whowechina/iidx_pico/cad/kailh-choc-stibilizer-4.jpg

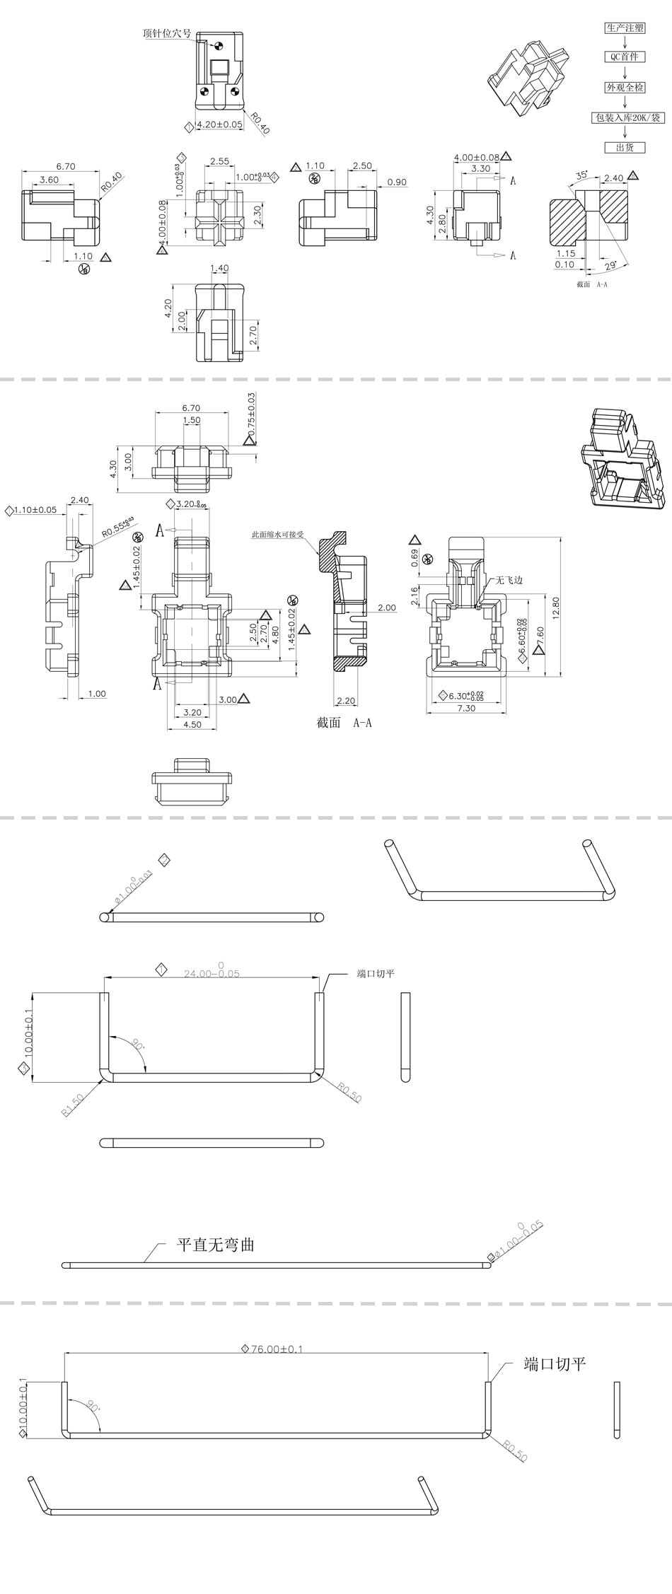
cad/kailh-choc-stibilizer-4.jpg
