whowechina/iidx_pico/PCB/Itsy/3dmodels/WS2812B.step

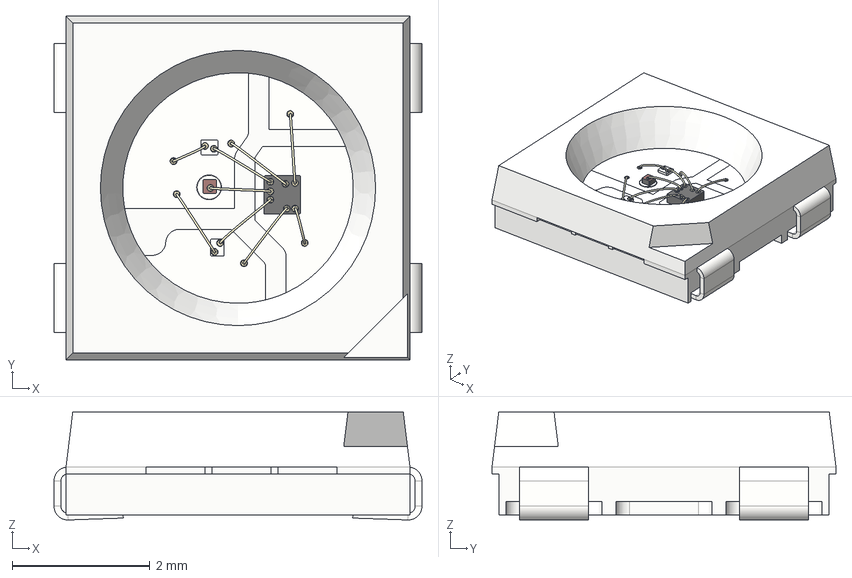
[picture p52: CAD file, 2023-04-01]
PCB/Itsy/3dmodels/WS2812B.step
5.35 x 5.00 x 1.57 mm
