whowechina/iidx_pico/PCB/Pico/3dmodels/SM3B-SRSS-TB.step

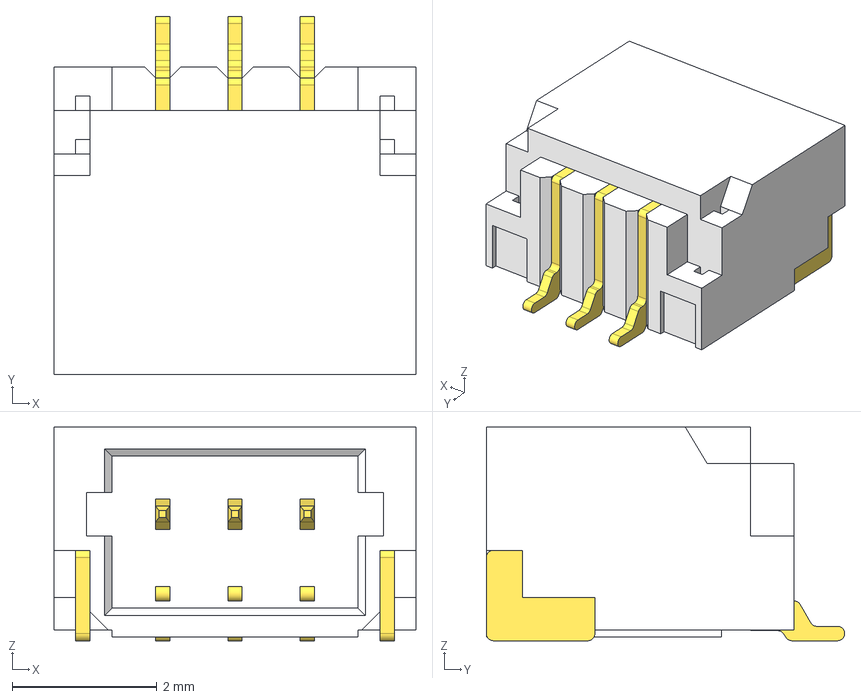
[picture p53: CAD file, 2024-11-20]
PCB/Pico/3dmodels/SM3B-SRSS-TB.step
5.00 x 4.95 x 2.95 mm
