whowechina/iidx_pico/Production/AcrylicCut/TT_disc_170.dxf

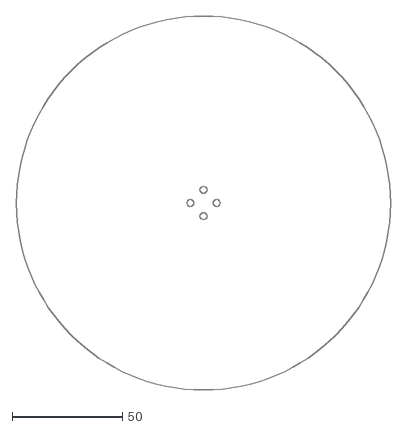
[picture p54: CAD file, 2023-04-01]
Production/AcrylicCut/TT_disc_170.dxf
170.0 x 170.0
