whowechina/iidx_pico/cad/keycap_frame_aux.stl

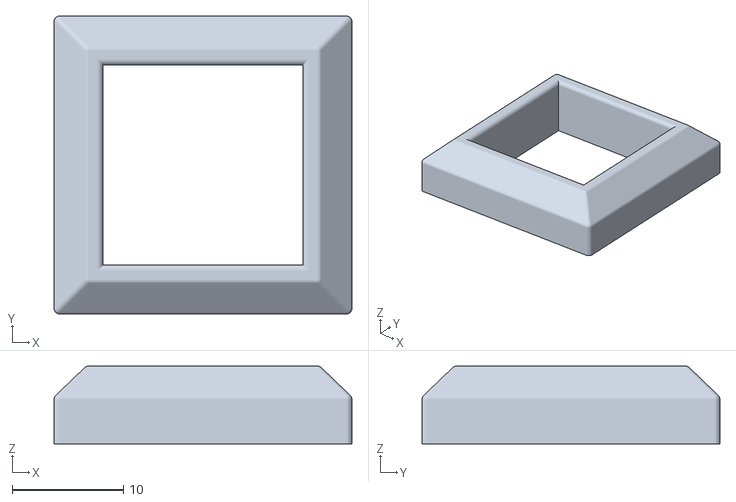
[picture p55: CAD file, 2023-04-01]
cad/keycap_frame_aux.stl
26.8 x 26.8 x 7.00
