whowechina/iidx_pico/Production/AcrylicCut/TT_disc_180.dxf

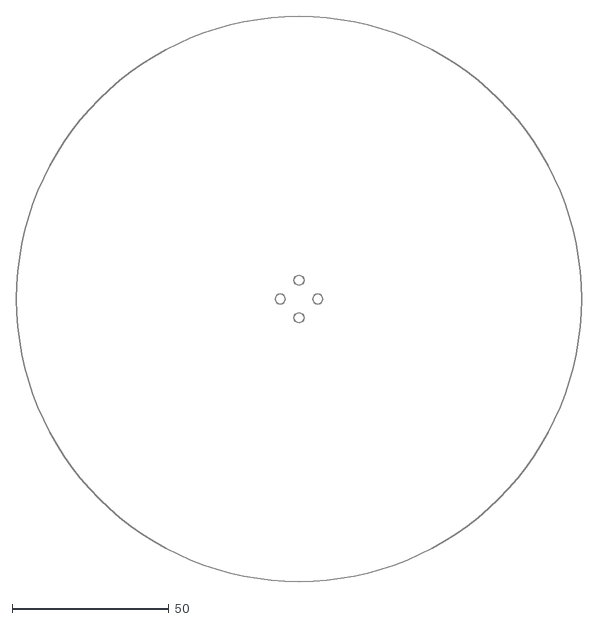
[picture p57: CAD file, 2023-04-01]
Production/AcrylicCut/TT_disc_180.dxf
180.0 x 180.0
