whowechina/iidx_pico/cad/pogo5f.stl

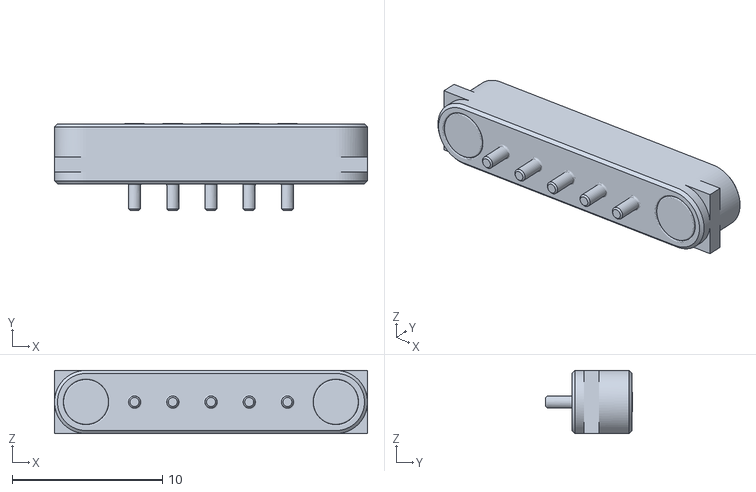
[picture p58: CAD file, 2023-04-01]
cad/pogo5f.stl
20.8 x 5.75 x 4.20
