whowechina/iidx_pico/PCB/Itsy/3dmodels/Magnetic Pogo Connector 5 Pin (M) - 副本.STEP

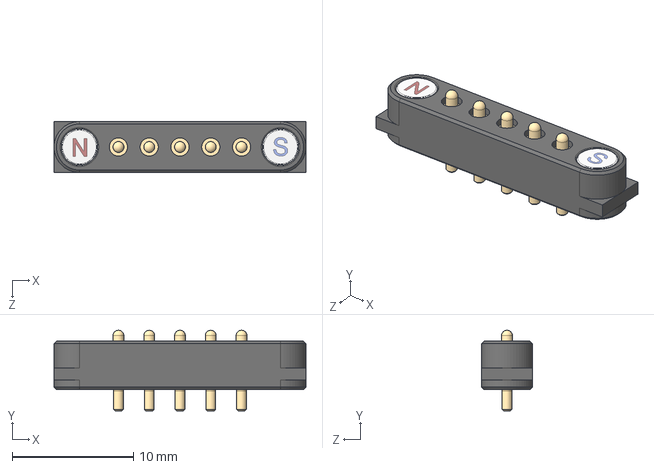
[picture p59: CAD file, 2023-04-01]
PCB/Itsy/3dmodels/Magnetic Pogo Connector 5 Pin (M) - 副本.STEP
20.8 x 6.65 x 4.20 mm
