whowechina/iidx_pico/Production/3DPrint/Turntable Itsy - Disc.stl

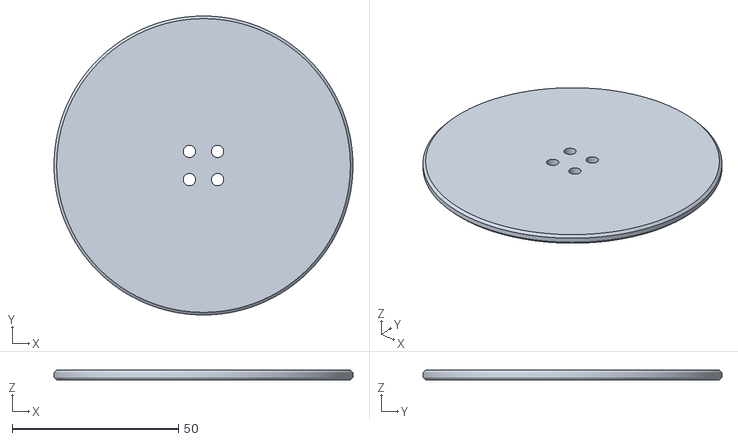
[picture p60: CAD file, 2026-05-16]
Production/3DPrint/Turntable Itsy - Disc.stl
90.0 x 90.0 x 3.00
