whowechina/iidx_pico/Production/AcrylicCut/TT_disc_150.dxf

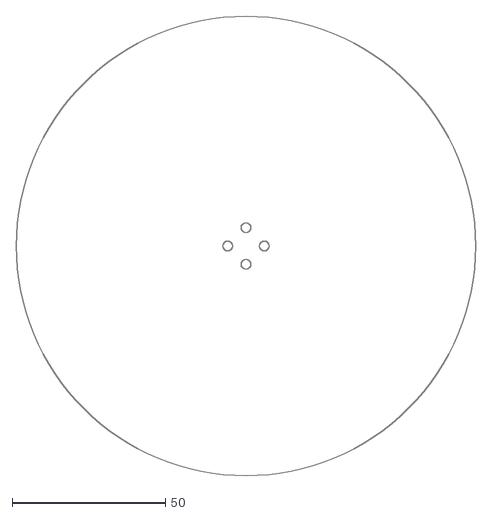
[picture p61: CAD file, 2023-04-01]
Production/AcrylicCut/TT_disc_150.dxf
150.0 x 150.0
