whowechina/iidx_pico/cad/beatmania_iidx.stl

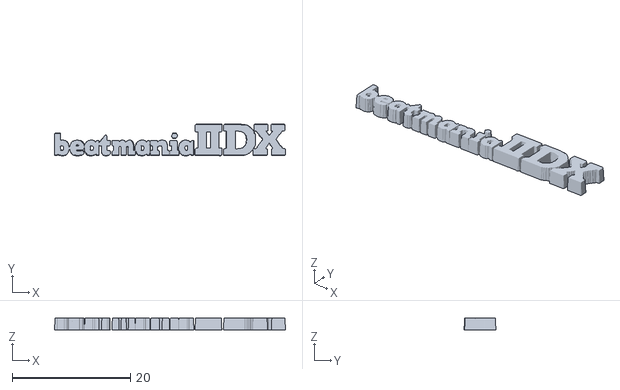
[picture p62: CAD file, 2023-04-01]
cad/beatmania_iidx.stl
39.0 x 5.38 x 2.00
