whowechina/iidx_pico/PCB/Itsy/3dmodels/SW_Hotswap_Kailh_MX.stp

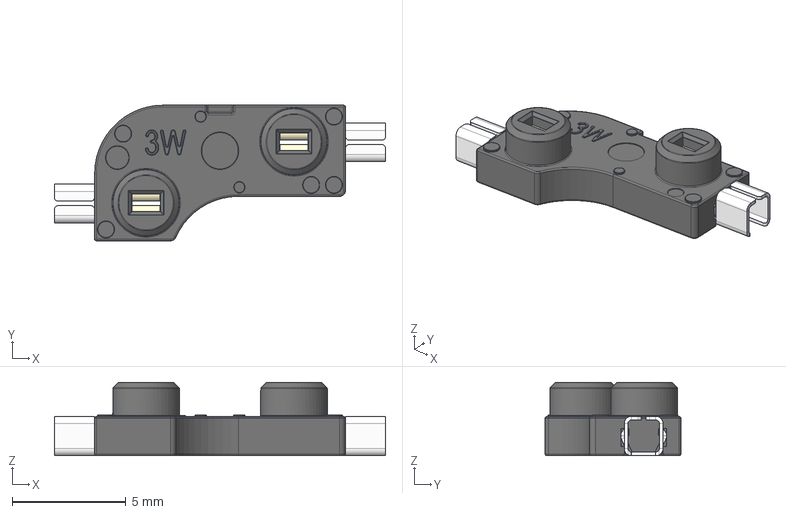
[picture p63: CAD file, 2023-04-01]
PCB/Itsy/3dmodels/SW_Hotswap_Kailh_MX.stp
14.5 x 5.95 x 3.22 mm
