whowechina/iidx_pico/Production/3DPrint/Keyboard Itsy - Base_1P.stl

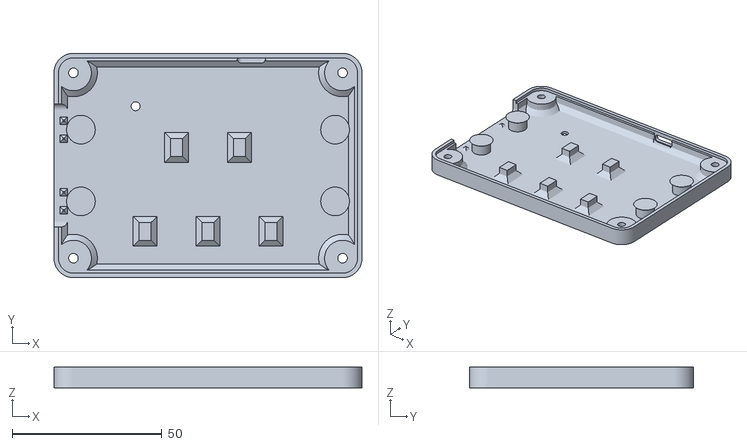
[picture p64: CAD file, 2026-05-16]
Production/3DPrint/Keyboard Itsy - Base_1P.stl
103.0 x 75.0 x 7.00
