whowechina/iidx_pico/PCB/Itsy/3dmodels/Magnetic Pogo Connector 5 Pin (Type 3).STEP

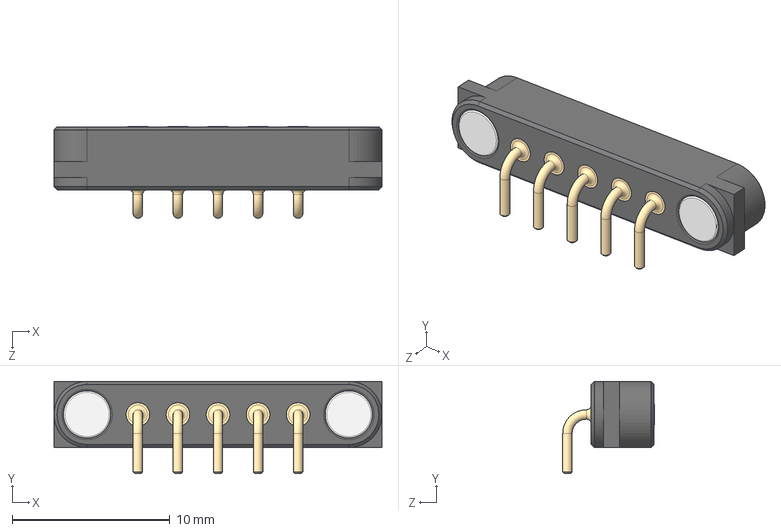
[picture p65: CAD file, 2023-04-01]
PCB/Itsy/3dmodels/Magnetic Pogo Connector 5 Pin (Type 3).STEP
20.8 x 5.85 x 5.80 mm
