whowechina/iidx_pico/Production/3DPrint/Keyboard Itsy - Panel.stl

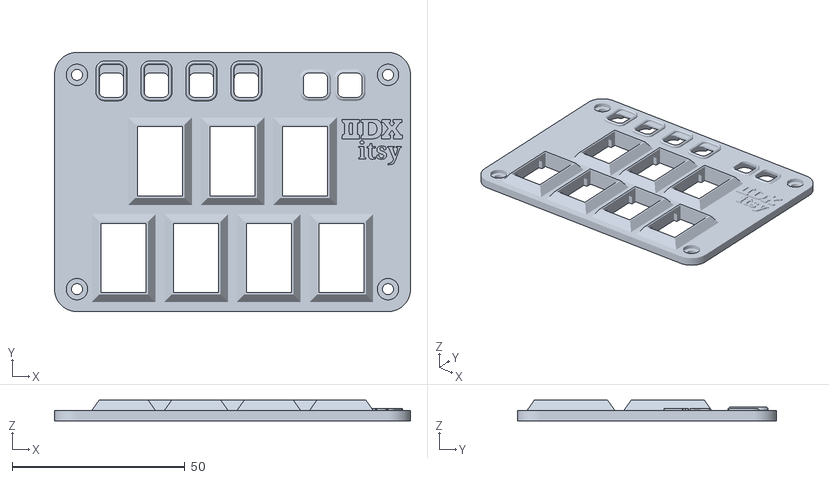
[picture p66: CAD file, 2026-05-16]
Production/3DPrint/Keyboard Itsy - Panel.stl
103.0 x 75.0 x 6.00
