whowechina/iidx_pico/cad/skf6805.stl

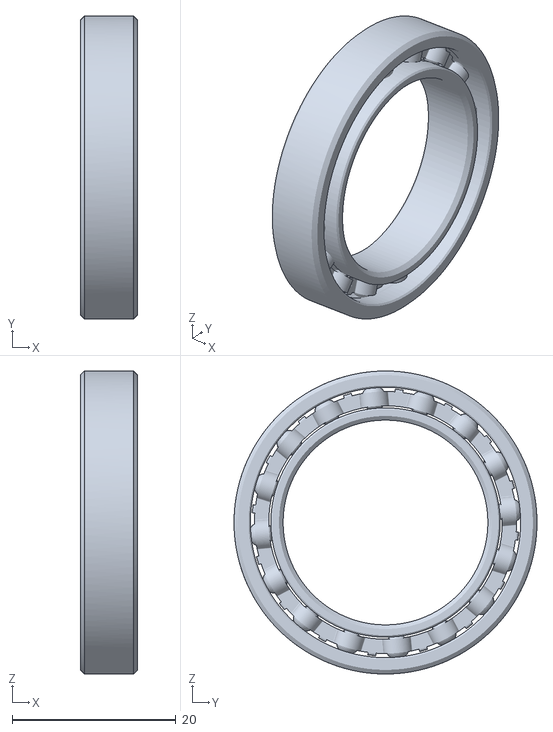
[picture p67: CAD file, 2023-04-01]
cad/skf6805.stl
7.00 x 37.0 x 37.0
