whowechina/iidx_pico/PCB/Itsy/3dmodels/J 2835.step

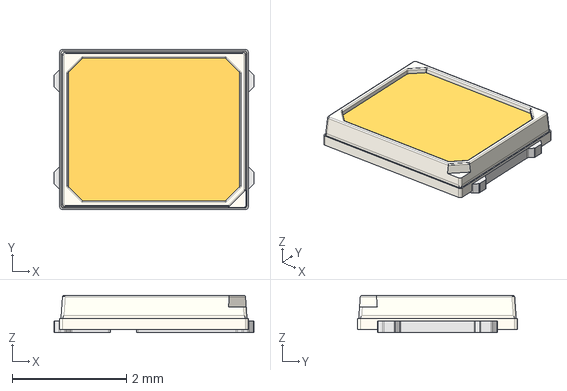
[picture p68: CAD file, 2023-04-01]
PCB/Itsy/3dmodels/J 2835.step
3.50 x 2.80 x 0.65 mm
