whowechina/iidx_pico/Production/3DPrint/Turntable Itsy - Banner.stl

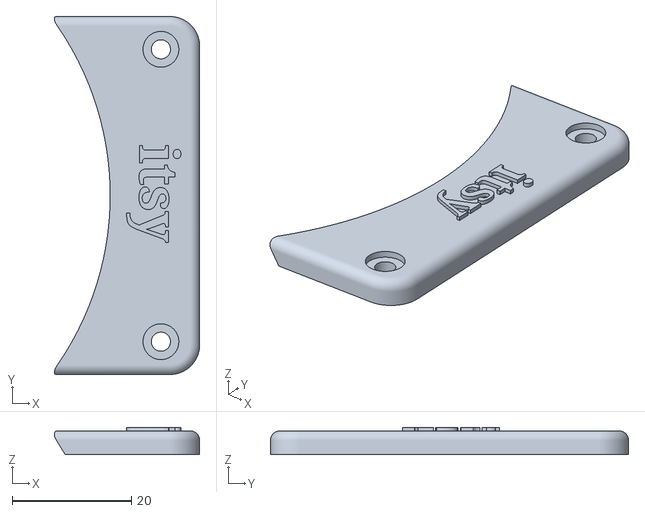
[picture p69: CAD file, 2026-05-16]
Production/3DPrint/Turntable Itsy - Banner.stl
24.4 x 60.0 x 4.60
