whowechina/iidx_pico/PCB/Itsy/3dmodels/WS2812-0807.STEP

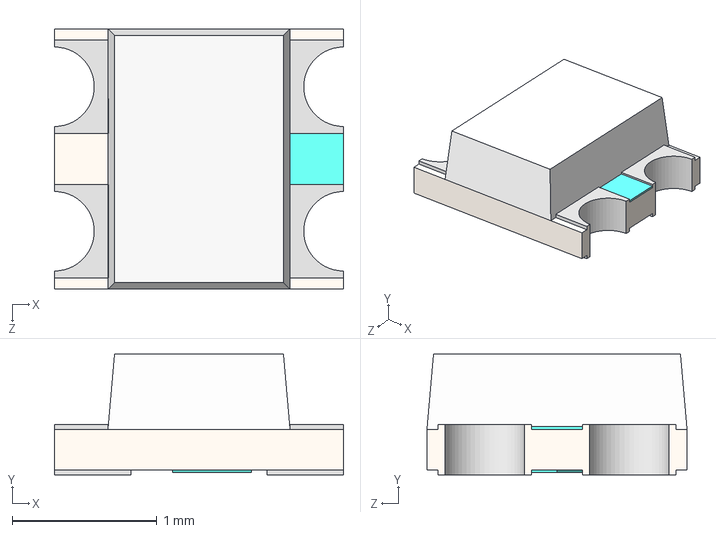
[picture p70: CAD file, 2023-04-01]
PCB/Itsy/3dmodels/WS2812-0807.STEP
2.00 x 0.835 x 1.80 mm
