whowechina/iidx_pico/PCB/Itsy/3dmodels/SW_Kailh_Choc_V1.stp

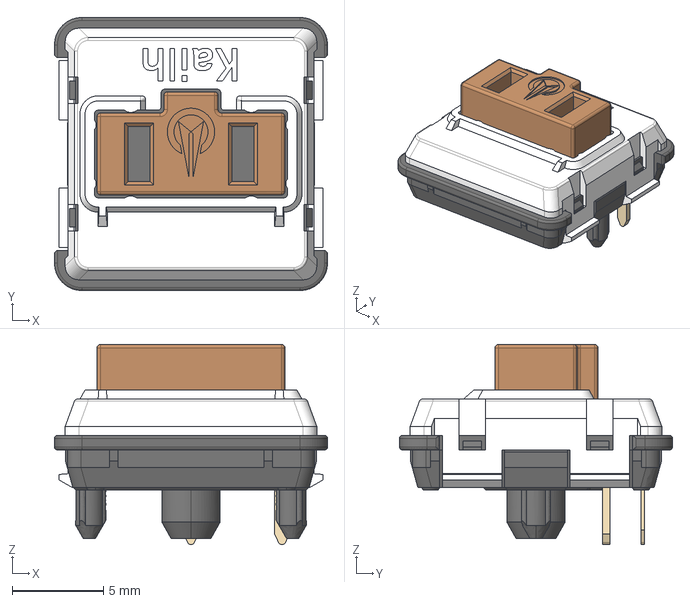
[picture p71: CAD file, 2023-04-01]
PCB/Itsy/3dmodels/SW_Kailh_Choc_V1.stp
15.0 x 15.0 x 11.0 mm
