whowechina/iidx_pico/Production/3DPrint/Keycap Itsy - Keycap.stl

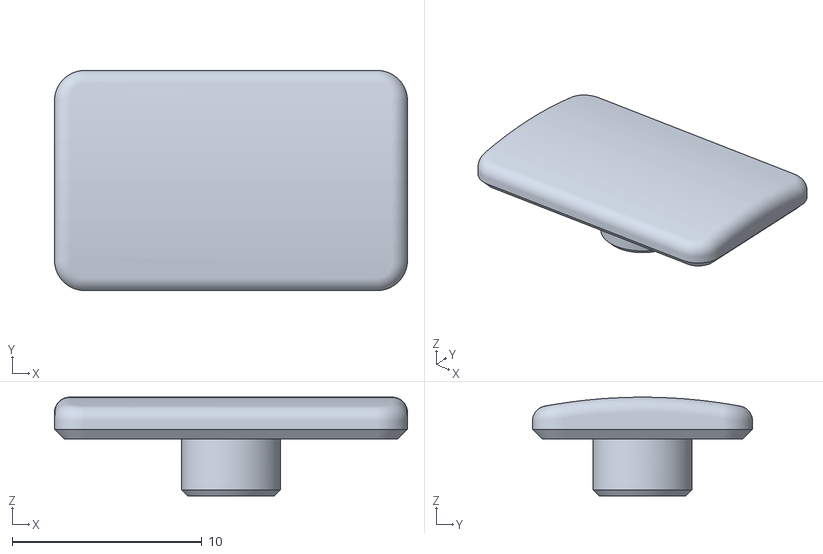
[picture p72: CAD file, 2026-05-16]
Production/3DPrint/Keycap Itsy - Keycap.stl
18.6 x 11.6 x 5.20
