whowechina/iidx_pico/PCB/Itsy/3dmodels/User Library-PTS645SL95SMTR92-LFS.STEP

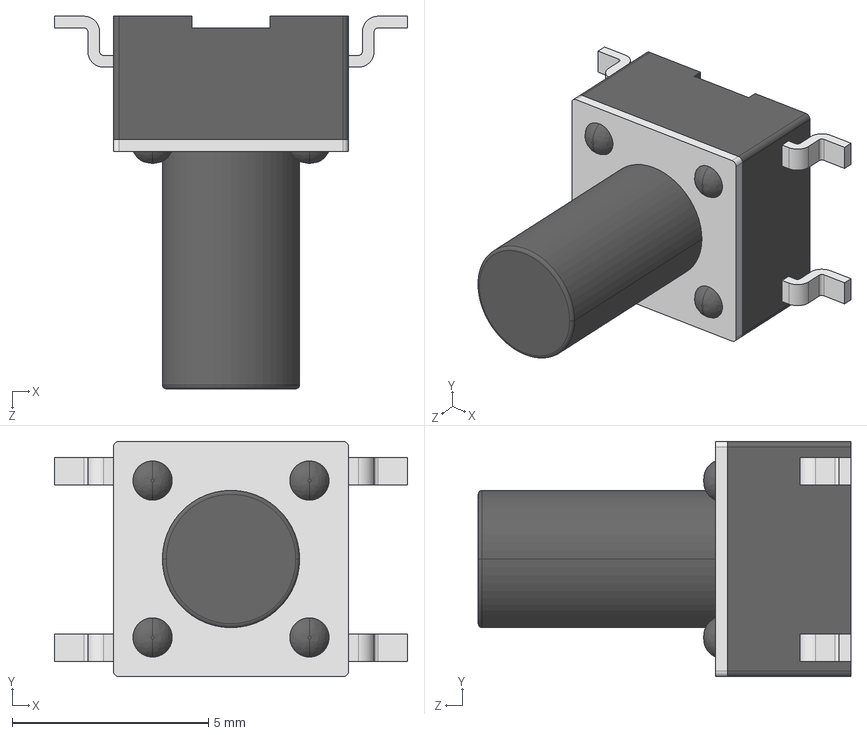
[picture p73: CAD file, 2023-04-01]
PCB/Itsy/3dmodels/User Library-PTS645SL95SMTR92-LFS.STEP
9.00 x 6.00 x 9.50 mm
