whowechina/iidx_pico/Production/3DPrint/Turntable Itsy - Base.stl

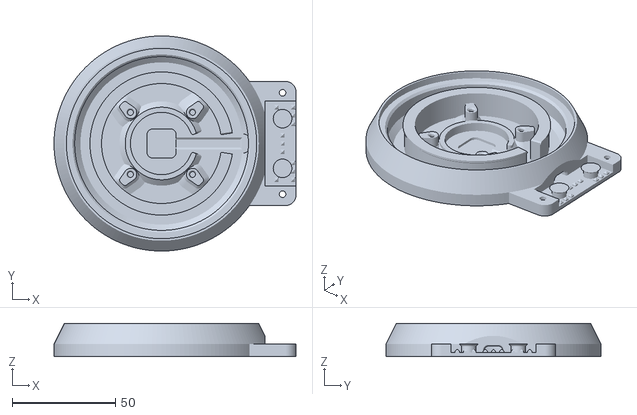
[picture p74: CAD file, 2026-05-16]
Production/3DPrint/Turntable Itsy - Base.stl
117.0 x 104.0 x 16.0
