whowechina/iidx_pico/PCB/Itsy/3dmodels/EVQ-P1D05M.stp

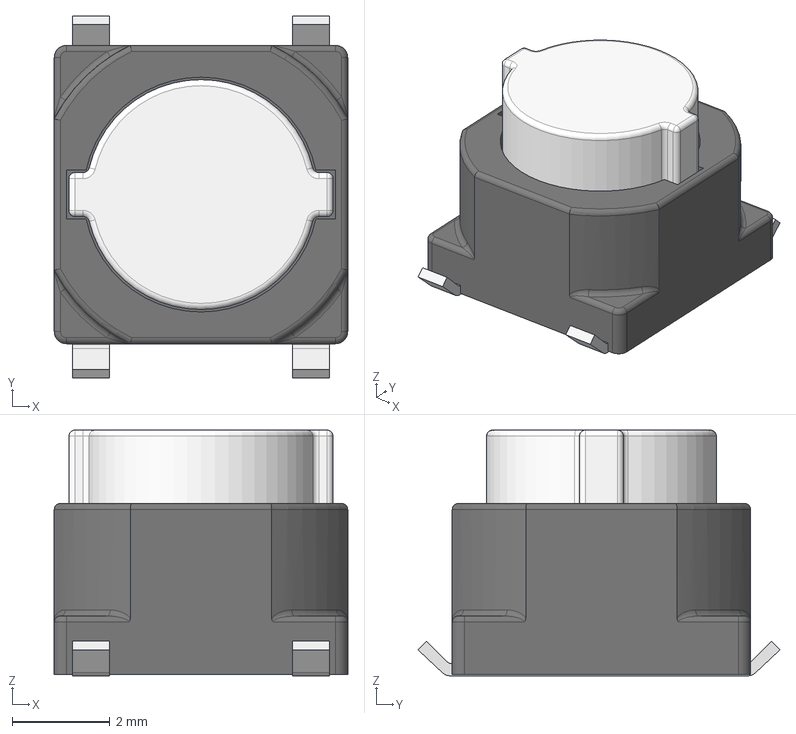
[picture p75: CAD file, 2023-04-01]
PCB/Itsy/3dmodels/EVQ-P1D05M.stp
6.00 x 7.40 x 5.03 mm
