whowechina/iidx_pico/Production/3DPrint/Turntable Jumbo - Disc.stl

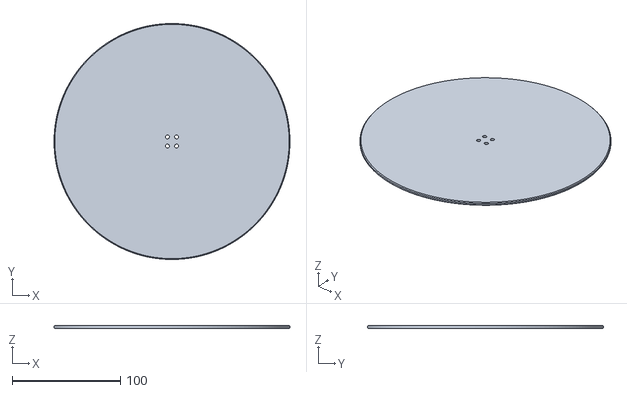
[picture p76: CAD file, 2026-03-05]
Production/3DPrint/Turntable Jumbo - Disc.stl
218.0 x 218.0 x 3.00
