whowechina/iidx_pico/PCB/Itsy/3dmodels/SMD WS2812B-3535.step

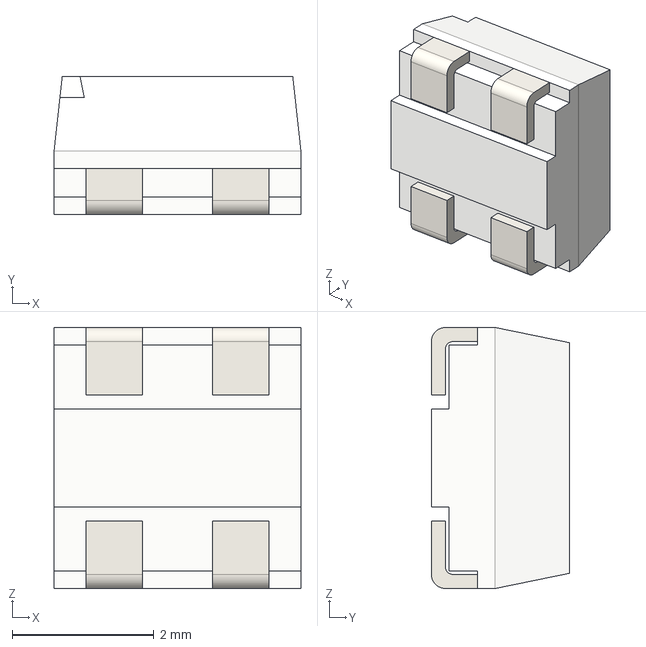
[picture p77: CAD file, 2023-04-01]
PCB/Itsy/3dmodels/SMD WS2812B-3535.step
3.48 x 1.95 x 3.68 mm
