whowechina/iidx_pico/Production/3DPrint/Turntable Teeny - Disc.stl

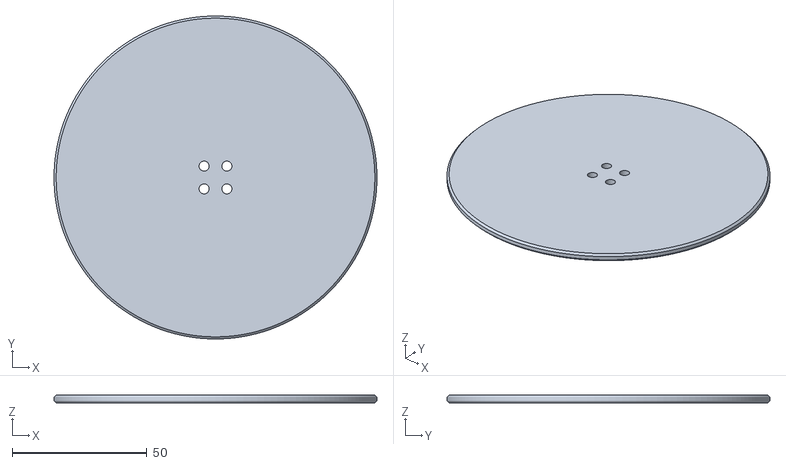
[picture p78: CAD file, 2026-03-05]
Production/3DPrint/Turntable Teeny - Disc.stl
120.0 x 120.0 x 3.00
