whowechina/iidx_pico/PCB/Itsy/3dmodels/User Library-WS2812-2020.step

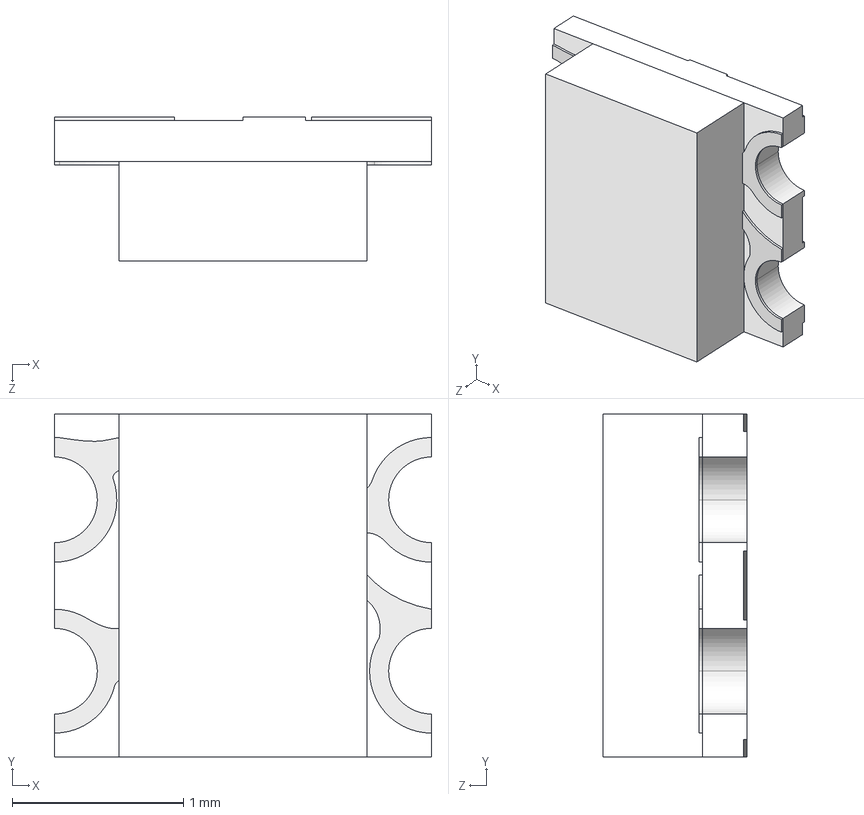
[picture p79: CAD file, 2023-04-01]
PCB/Itsy/3dmodels/User Library-WS2812-2020.step
2.20 x 2.00 x 0.84 mm
