whowechina/iidx_pico/Production/3DPrint/Turntable Pico - Disc.stl

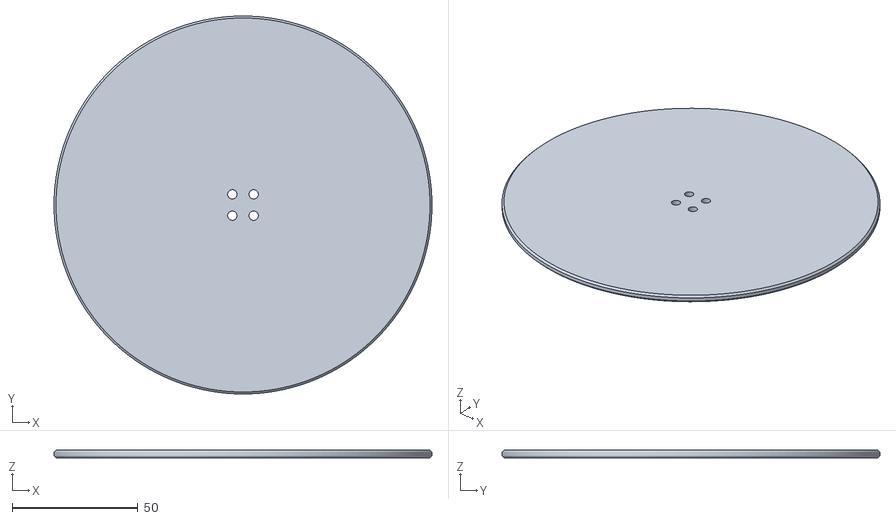
[picture p80: CAD file, 2026-03-05]
Production/3DPrint/Turntable Pico - Disc.stl
150.0 x 150.0 x 3.00
