whowechina/iidx_pico/PCB/Itsy/3dmodels/Kailh LP Choc PC Keycap.step

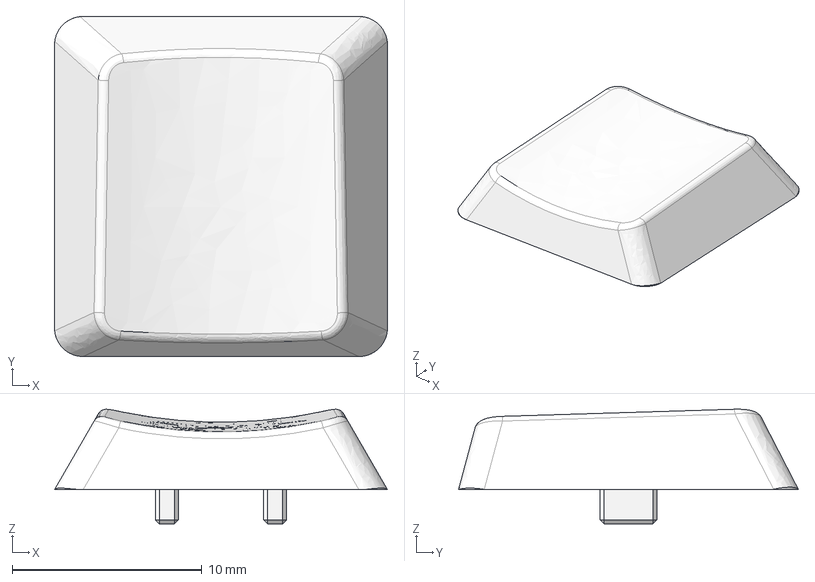
[picture p81: CAD file, 2023-04-01]
PCB/Itsy/3dmodels/Kailh LP Choc PC Keycap.step
17.5 x 17.9 x 6.03 mm
