whowechina/iidx_pico/Production/3DPrint/Turntable Jumbo 1P - Banner.stl

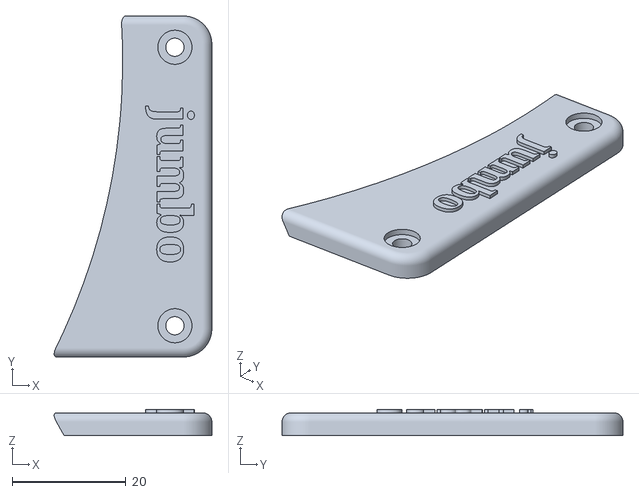
[picture p82: CAD file, 2025-11-17]
Production/3DPrint/Turntable Jumbo 1P - Banner.stl
27.7 x 60.0 x 4.60
