whowechina/iidx_pico/PCB/Itsy/3dmodels/User Library-WS2812-4020.step

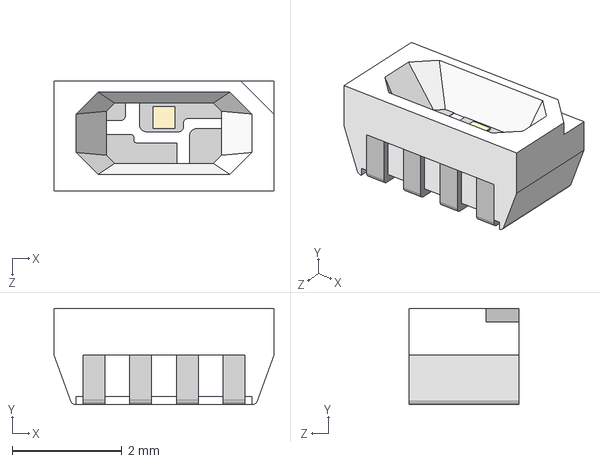
[picture p83: CAD file, 2023-04-01]
PCB/Itsy/3dmodels/User Library-WS2812-4020.step
4.00 x 1.75 x 2.00 mm
