whowechina/iidx_pico/Production/3DPrint/Turntable Teeny - Banner.stl

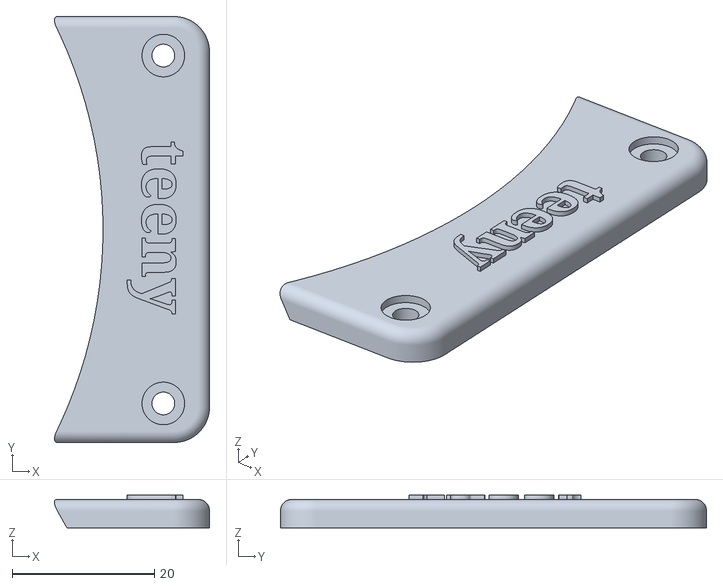
[picture p84: CAD file, 2025-11-17]
Production/3DPrint/Turntable Teeny - Banner.stl
21.8 x 60.0 x 4.60
