whowechina/iidx_pico/PCB/Itsy/3dmodels/WS2812-2020.STEP

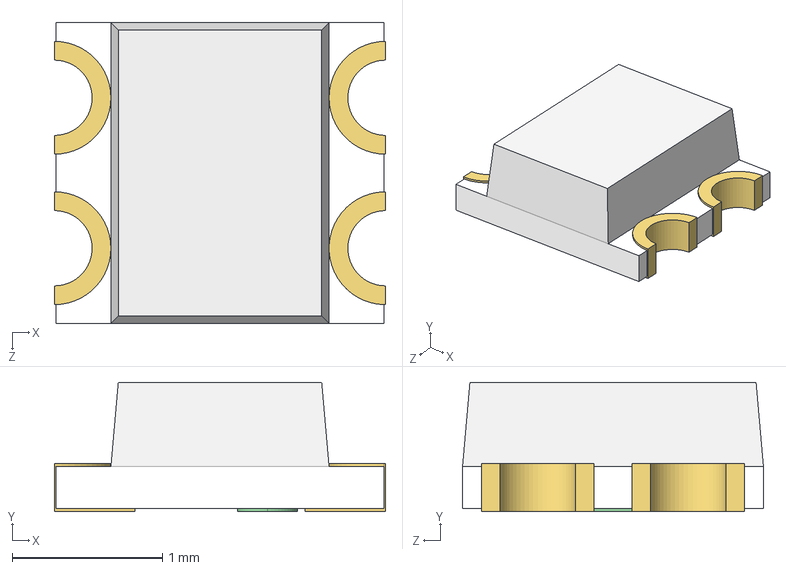
[picture p85: CAD file, 2023-04-01]
PCB/Itsy/3dmodels/WS2812-2020.STEP
2.20 x 0.86 x 2.00 mm
