whowechina/iidx_pico/Production/3DPrint/Keyboard DP - Base.stl

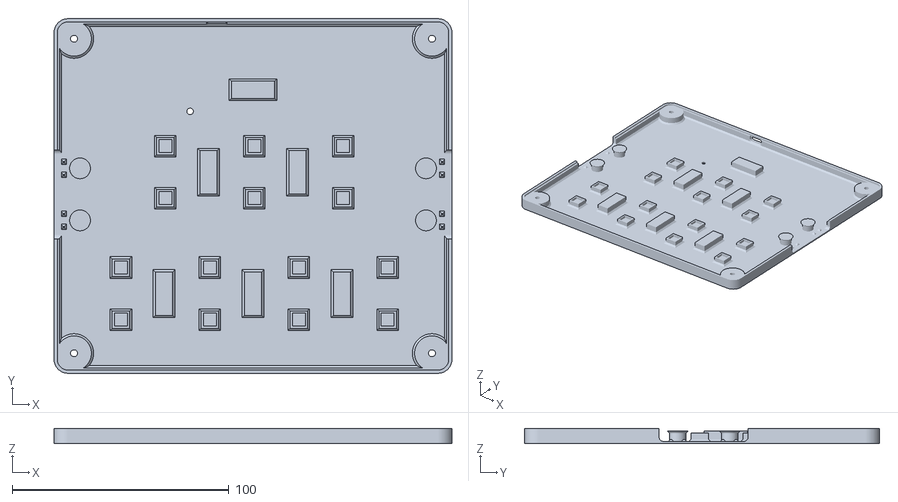
[picture p86: CAD file, 2025-11-17]
Production/3DPrint/Keyboard DP - Base.stl
183.5 x 163.5 x 7.00
