whowechina/iidx_pico/Production/3DPrint/Keyboard Teeny 1P - Base.stl

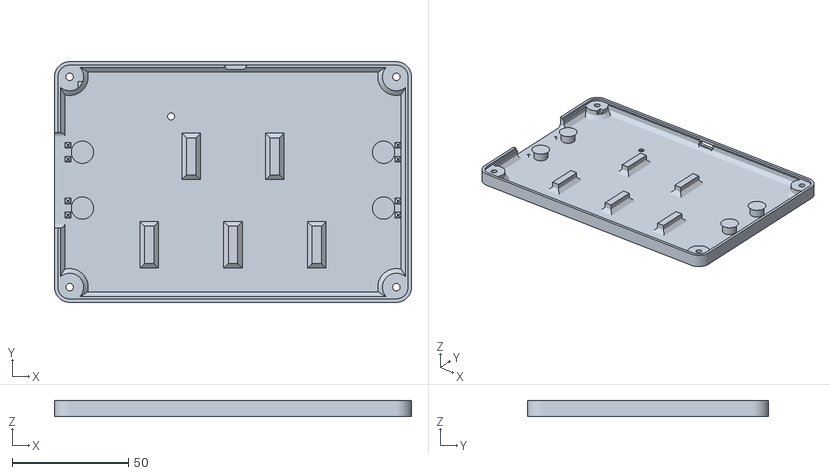
[picture p87: CAD file, 2025-11-17]
Production/3DPrint/Keyboard Teeny 1P - Base.stl
153.4 x 103.4 x 7.00
