whowechina/iidx_pico/PCB/Itsy/3dmodels/Magnetic Pogo Connector 5 Pin (Type 4).STEP

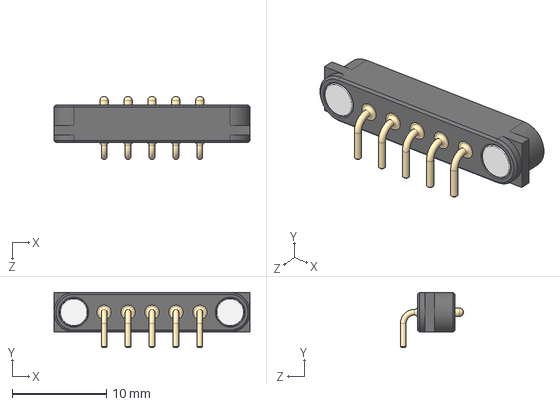
[picture p88: CAD file, 2023-04-01]
PCB/Itsy/3dmodels/Magnetic Pogo Connector 5 Pin (Type 4).STEP
20.8 x 5.85 x 6.70 mm
