whowechina/iidx_pico/Production/3DPrint/Turntable Pico - Banner.stl

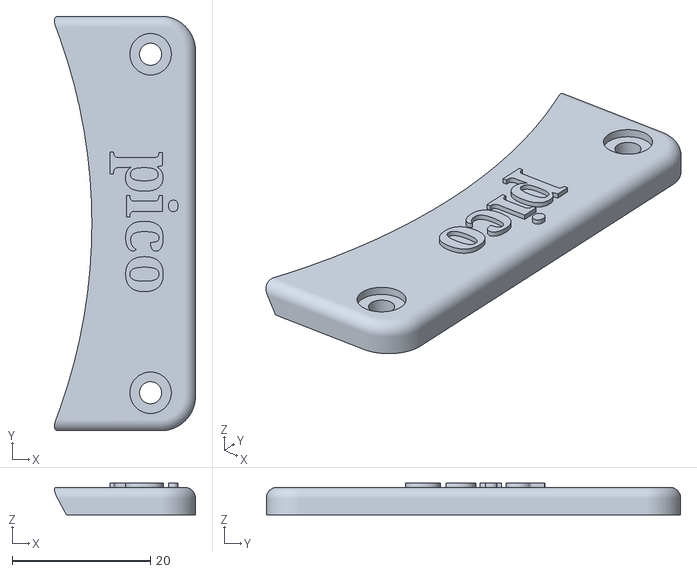
[picture p89: CAD file, 2025-11-17]
Production/3DPrint/Turntable Pico - Banner.stl
20.4 x 60.0 x 4.60
