whowechina/iidx_pico/PCB/Itsy/3dmodels/Tact Switch 4.5mm SMT.step

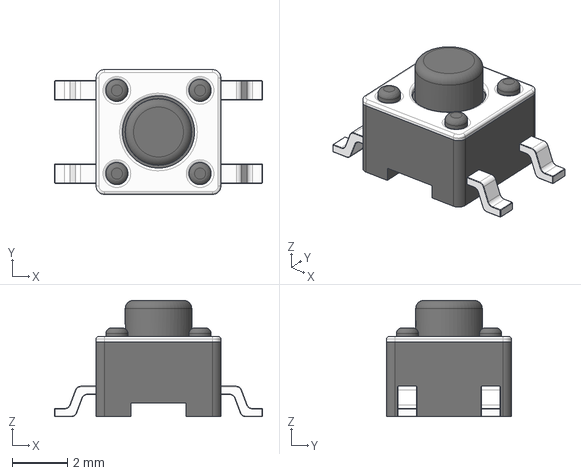
[picture p90: CAD file, 2023-04-01]
PCB/Itsy/3dmodels/Tact Switch 4.5mm SMT.step
7.50 x 4.50 x 4.20 mm
