whowechina/iidx_pico/Production/3DPrint/Keycap - Pico Hall.stl

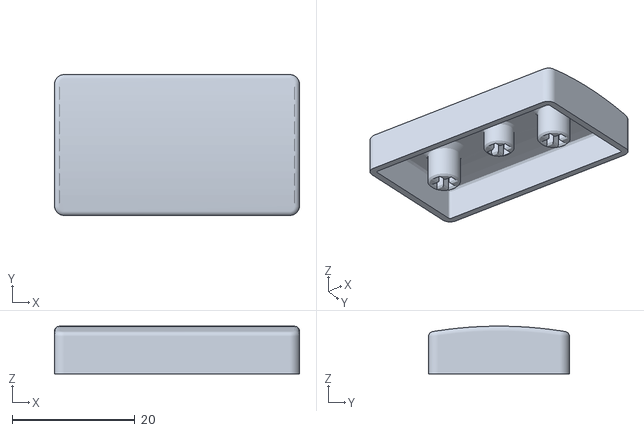
[picture p91: CAD file, 2025-09-27]
Production/3DPrint/Keycap - Pico Hall.stl
40.0 x 23.0 x 7.80
