whowechina/iidx_pico/Production/3DPrint/Keycap - Pico Choc V2.stl

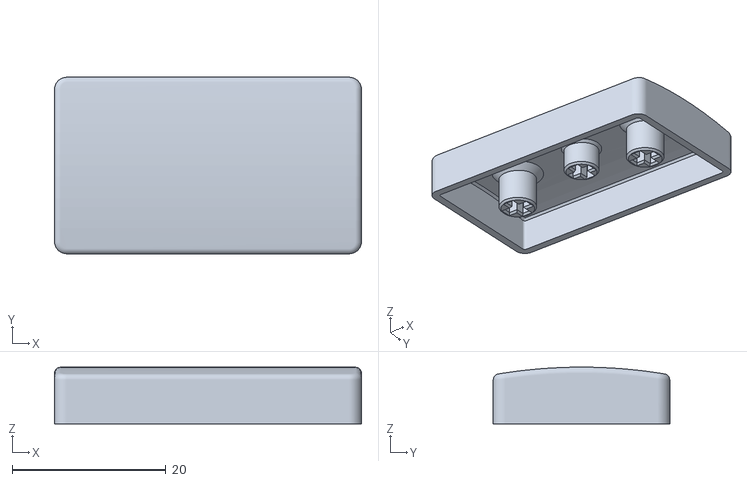
[picture p92: CAD file, 2025-09-27]
Production/3DPrint/Keycap - Pico Choc V2.stl
40.0 x 23.0 x 7.40
