whowechina/iidx_pico/Production/3DPrint/Keycap - Teeny Choc V2.stl

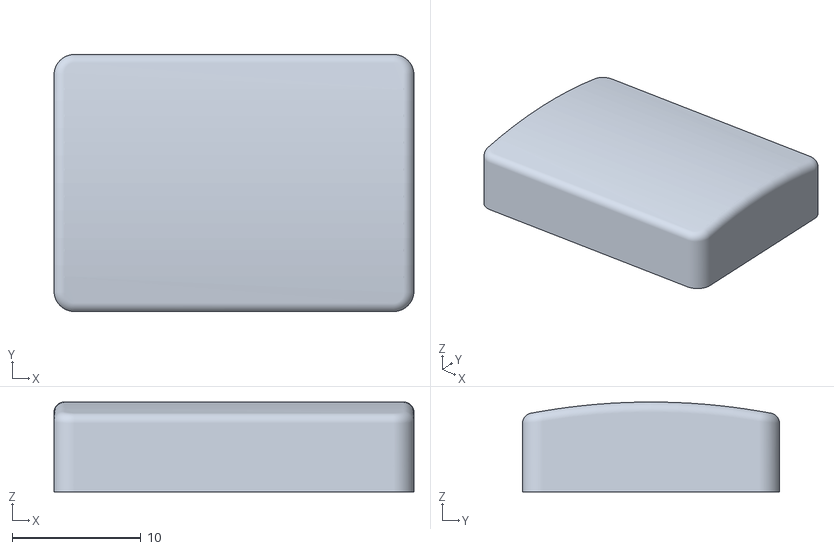
[picture p93: CAD file, 2025-09-27]
Production/3DPrint/Keycap - Teeny Choc V2.stl
28.0 x 20.0 x 7.00
