whowechina/iidx_pico/Production/3DPrint/Turntable Pico - Base.stl

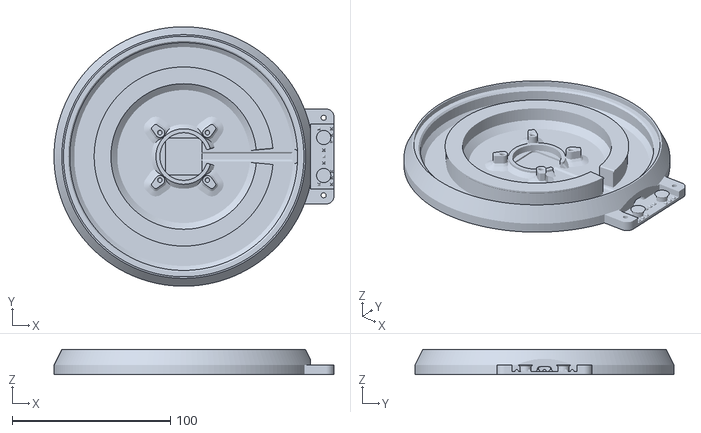
[picture p94: CAD file, 2025-02-22]
Production/3DPrint/Turntable Pico - Base.stl
177.0 x 164.0 x 16.0
