whowechina/iidx_pico/Production/3DPrint/Turntable Jumbo 2P - Base.stl

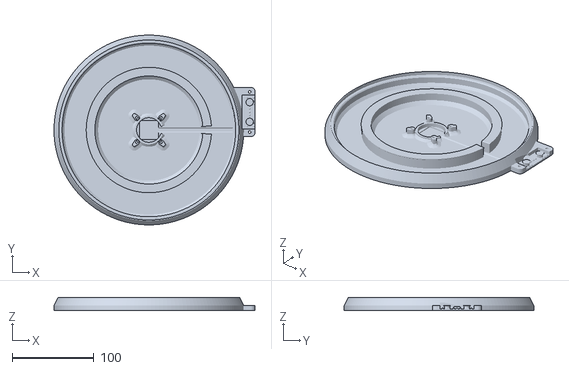
[picture p95: CAD file, 2025-02-22]
Production/3DPrint/Turntable Jumbo 2P - Base.stl
245.7 x 232.0 x 16.0
