whowechina/iidx_pico/Production/3DPrint/Turntable Teeny - Base.stl

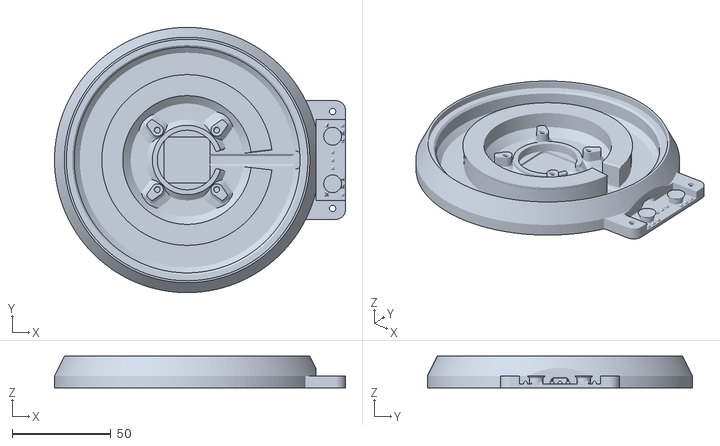
[picture p96: CAD file, 2025-02-22]
Production/3DPrint/Turntable Teeny - Base.stl
147.0 x 134.0 x 16.0
