whowechina/iidx_pico/Production/3DPrint/Keyboard Teeny - Panel.stl

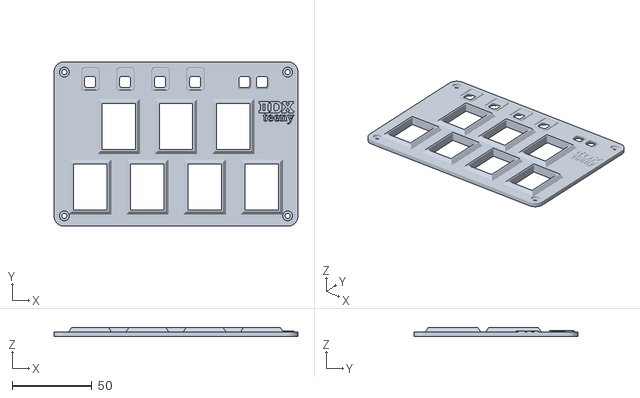
[picture p97: CAD file, 2025-02-09]
Production/3DPrint/Keyboard Teeny - Panel.stl
153.4 x 103.4 x 5.80
