whowechina/iidx_pico/Production/3DPrint/Turntable 2B - Bearing Seat.stl

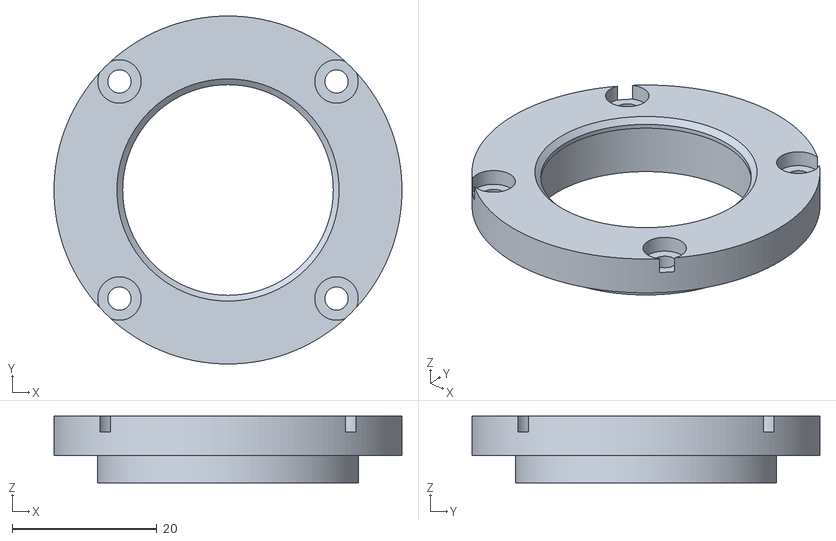
[picture p98: CAD file, 2025-02-09]
Production/3DPrint/Turntable 2B - Bearing Seat.stl
48.1 x 48.1 x 9.20
