whowechina/iidx_pico/Production/3DPrint/Turntable 2B - Magnet Seat.stl

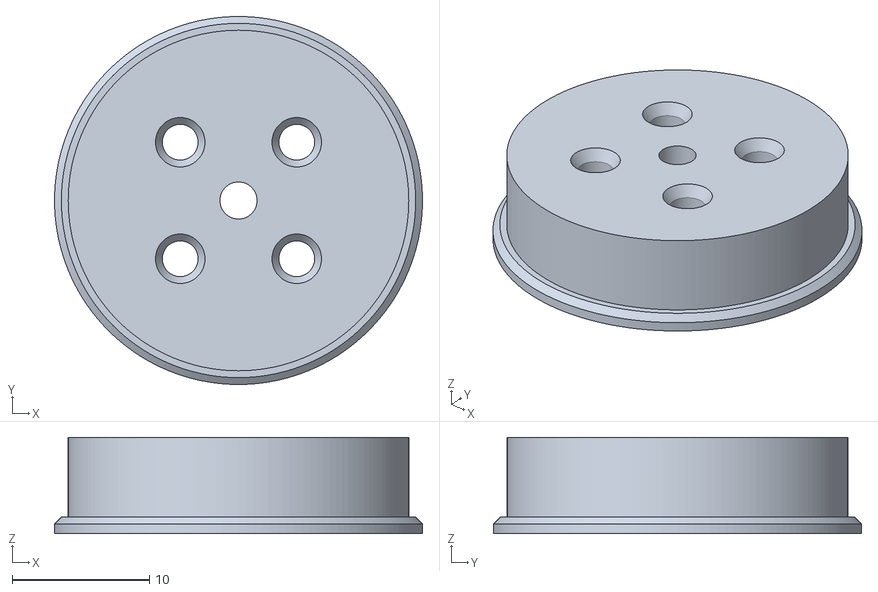
[picture p99: CAD file, 2025-01-16]
Production/3DPrint/Turntable 2B - Magnet Seat.stl
26.8 x 26.8 x 7.00
