whowechina/iidx_pico/Production/3DPrint/Turntable 2B - Disc Seat.stl

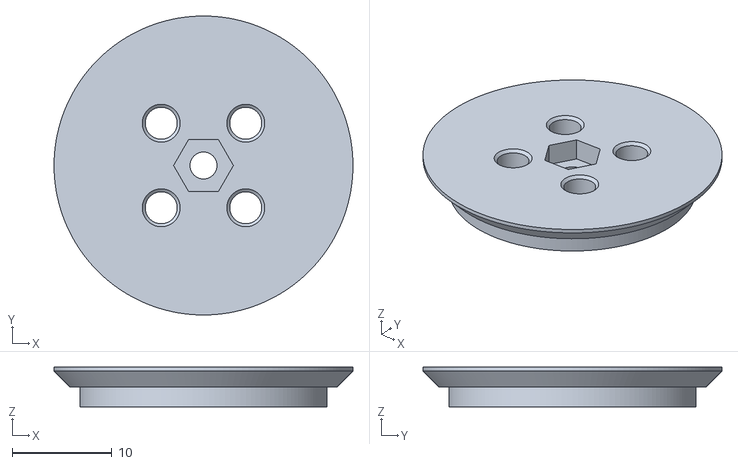
[picture p100: CAD file, 2025-01-16]
Production/3DPrint/Turntable 2B - Disc Seat.stl
30.0 x 30.0 x 4.00
