whowechina/iidx_pico/Production/3DPrint/Turntable - Magnet Seat.stl

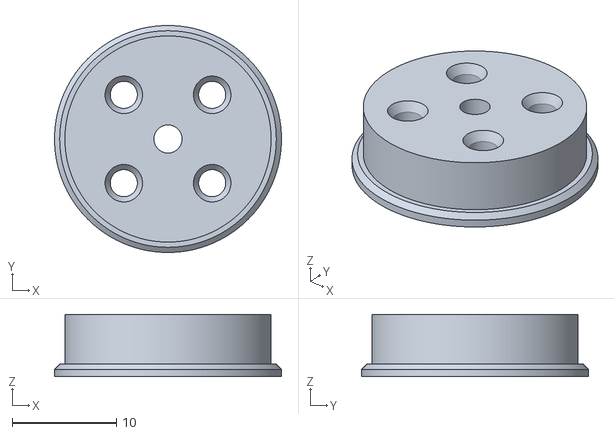
[picture p101: CAD file, 2024-12-21]
Production/3DPrint/Turntable - Magnet Seat.stl
21.8 x 21.8 x 6.00
