whowechina/iidx_pico/Production/3DPrint/Turntable - Disc Seat.stl

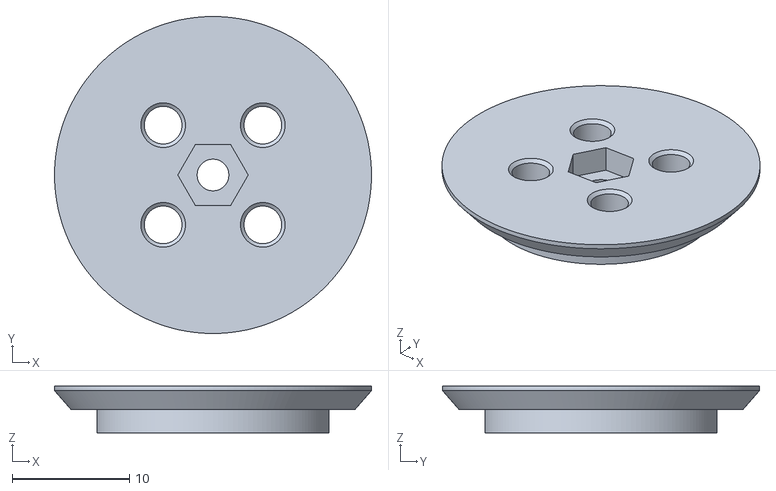
[picture p102: CAD file, 2024-12-21]
Production/3DPrint/Turntable - Disc Seat.stl
27.0 x 27.0 x 4.00
