whowechina/iidx_pico/Production/3DPrint/Turntable - Bearing Seat.stl

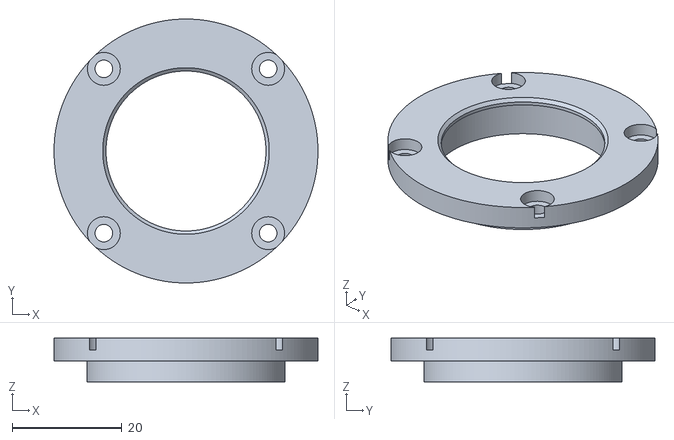
[picture p103: CAD file, 2024-12-19]
Production/3DPrint/Turntable - Bearing Seat.stl
48.2 x 48.2 x 8.00
