whowechina/iidx_pico/Production/3DPrint/bearing_seat_6804_hinge.stl

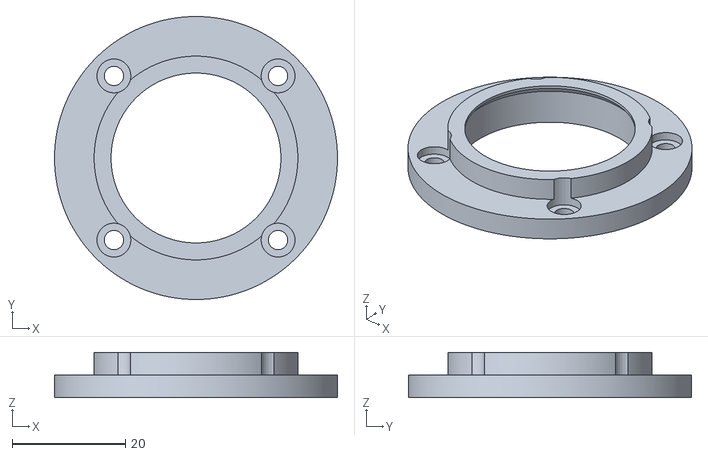
[picture p104: CAD file, 2023-10-05]
Production/3DPrint/bearing_seat_6804_hinge.stl
50.0 x 50.0 x 8.00
