whowechina/iidx_pico/Production/3DPrint/pcb_bottom_right_hinge.stl

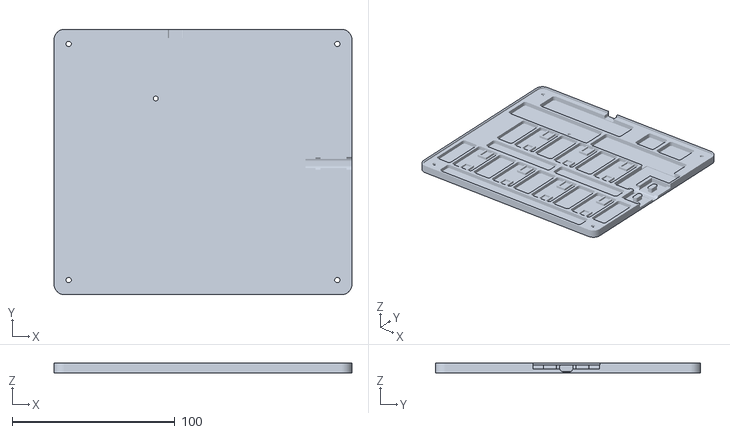
[picture p105: CAD file, 2023-08-06]
Production/3DPrint/pcb_bottom_right_hinge.stl
183.0 x 163.0 x 6.40
