whowechina/iidx_pico/Production/3DPrint/TT_base_hinge_cover_170.stl

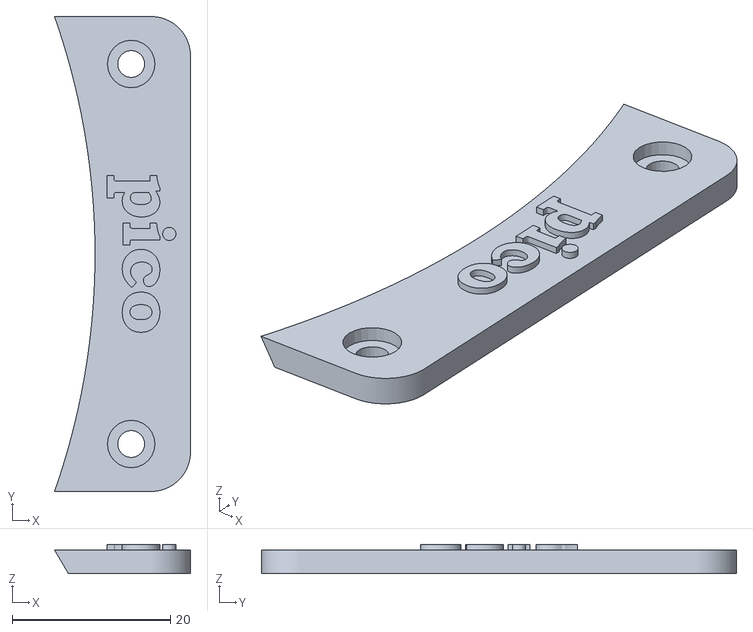
[picture p106: CAD file, 2023-08-06]
Production/3DPrint/TT_base_hinge_cover_170.stl
17.2 x 60.0 x 3.70
