whowechina/iidx_pico/Production/3DPrint/TT_base_hinge_cover_150.stl

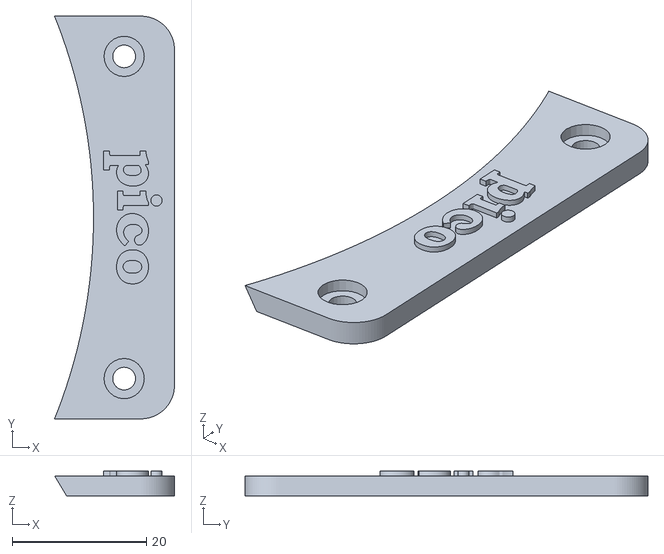
[picture p107: CAD file, 2023-08-06]
Production/3DPrint/TT_base_hinge_cover_150.stl
17.9 x 60.0 x 3.70
