whowechina/iidx_pico/Production/3DPrint/TT_base_hinge_170.stl

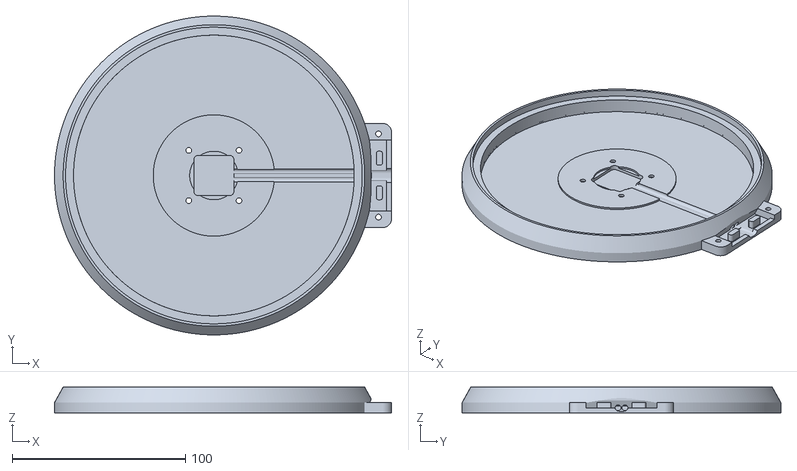
[picture p108: CAD file, 2023-08-06]
Production/3DPrint/TT_base_hinge_170.stl
194.5 x 184.0 x 15.0
