whowechina/iidx_pico/Production/3DPrint/TT_base_hinge_150.stl

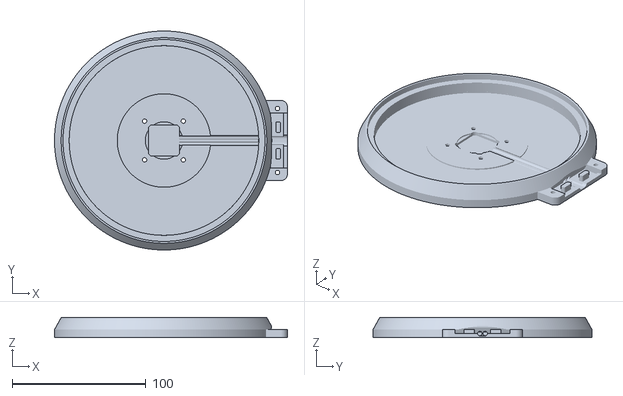
[picture p109: CAD file, 2023-08-06]
Production/3DPrint/TT_base_hinge_150.stl
174.5 x 164.0 x 15.0
