whowechina/iidx_pico/Production/3DPrint/iidx_keycap_choc_v2_fdm.stl

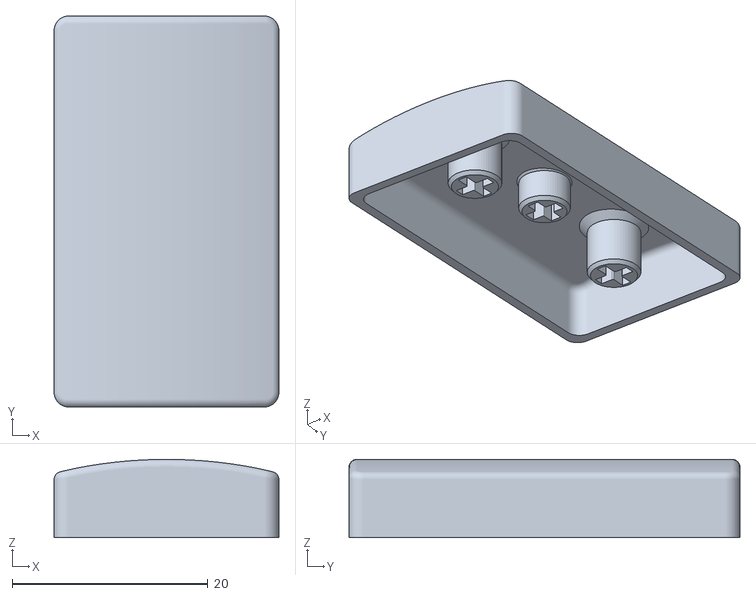
[picture p110: CAD file, 2023-04-22]
Production/3DPrint/iidx_keycap_choc_v2_fdm.stl
23.0 x 40.0 x 8.00
