whowechina/iidx_pico/Production/3DPrint/TTshaft_6805.stl

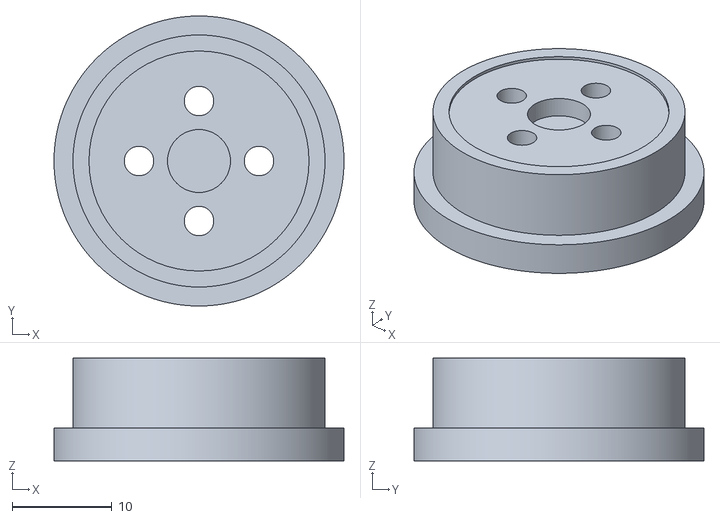
[picture p111: CAD file, 2023-04-04]
Production/3DPrint/TTshaft_6805.stl
29.0 x 29.0 x 10.3
