whowechina/iidx_pico/Production/3DPrint/TTshaft_6804.stl

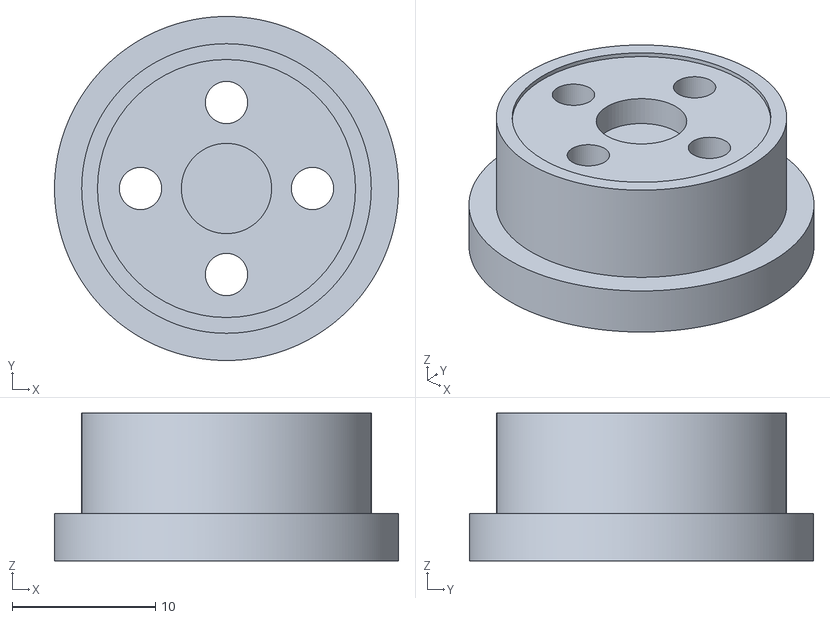
[picture p112: CAD file, 2023-04-04]
Production/3DPrint/TTshaft_6804.stl
24.0 x 24.0 x 10.3
