whowechina/iidx_pico/Production/3DPrint/iidx_keycap_choc_v2_sla.stl

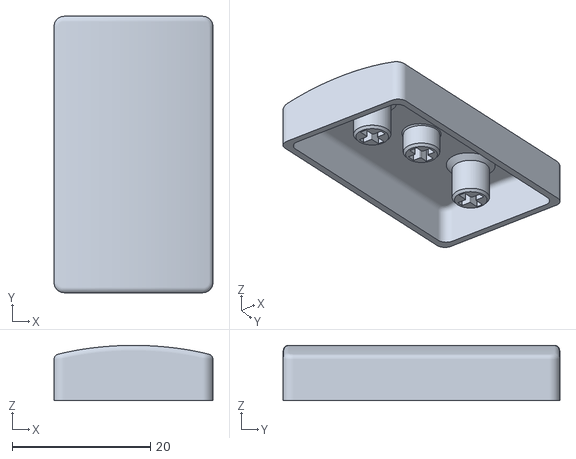
[picture p113: CAD file, 2023-04-04]
Production/3DPrint/iidx_keycap_choc_v2_sla.stl
23.0 x 40.0 x 8.00
