whowechina/iidx_pico/Production/3DPrint/bearing_seat_6805.stl

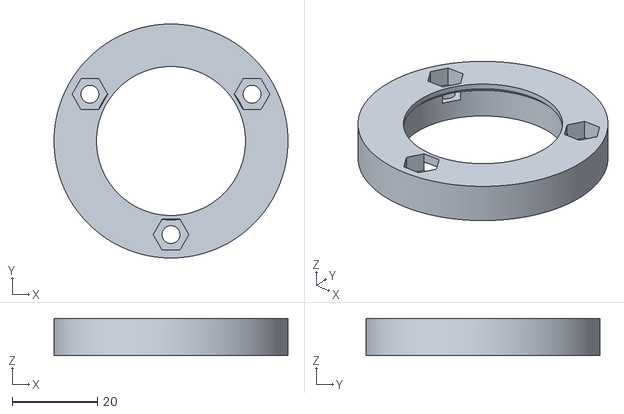
[picture p115: CAD file, 2023-04-02]
Production/3DPrint/bearing_seat_6805.stl
55.0 x 55.0 x 8.70
