whowechina/iidx_pico/Production/3DPrint/TT_base_180.stl

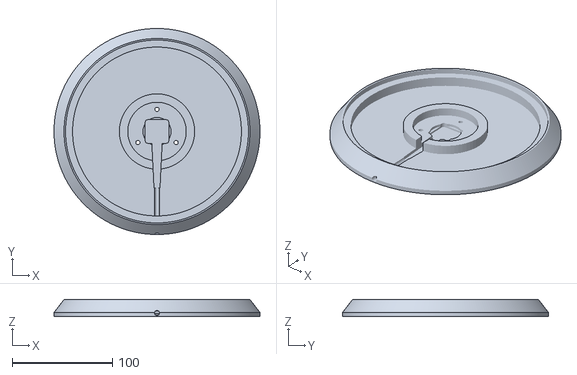
[picture p116: CAD file, 2023-04-01]
Production/3DPrint/TT_base_180.stl
205.0 x 205.0 x 17.0
