whowechina/iidx_pico/Production/3DPrint/pcb_top.stl

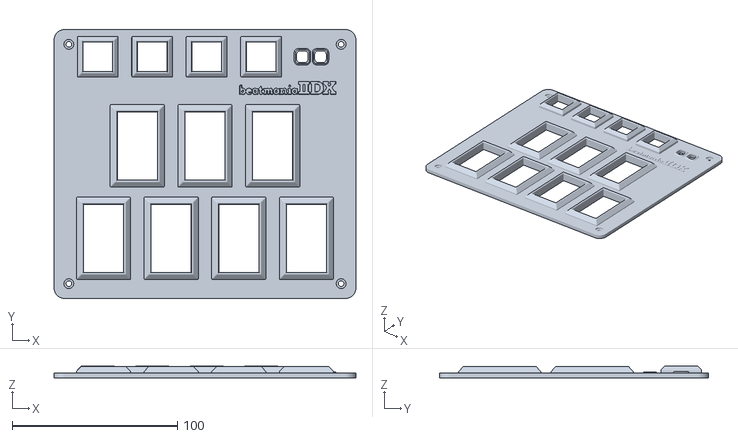
[picture p117: CAD file, 2023-04-01]
Production/3DPrint/pcb_top.stl
183.0 x 163.0 x 7.24
