whowechina/iidx_pico/Production/3DPrint/TT_base_150.stl

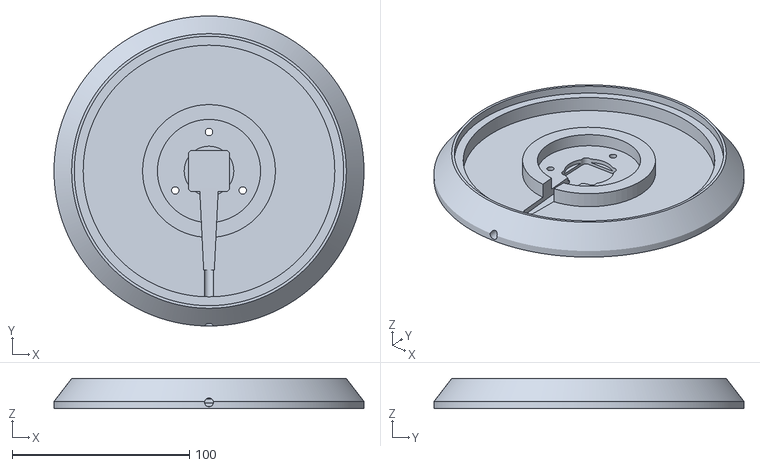
[picture p118: CAD file, 2023-04-01]
Production/3DPrint/TT_base_150.stl
175.0 x 175.0 x 17.0
