whowechina/iidx_pico/Production/3DPrint/TT_base_170.stl

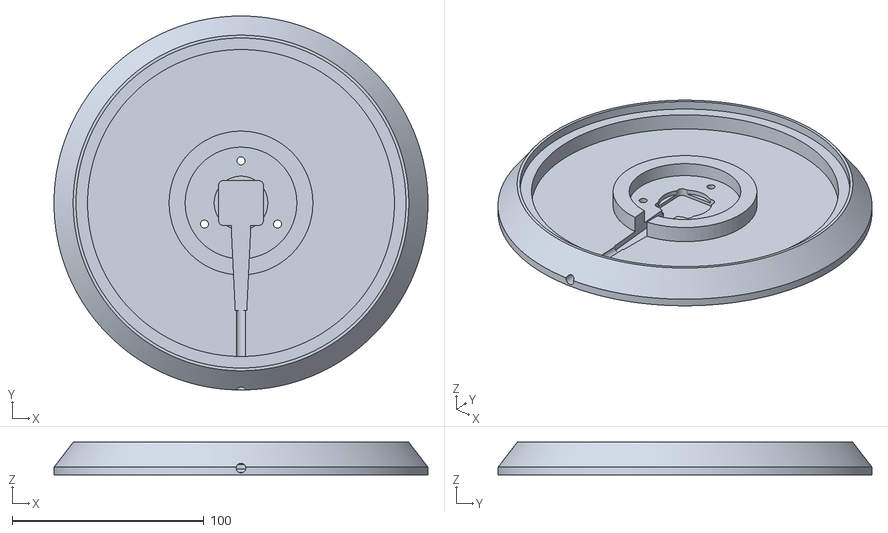
[picture p119: CAD file, 2023-04-01]
Production/3DPrint/TT_base_170.stl
195.0 x 195.0 x 17.0
