whowechina/iidx_pico/Production/3DPrint/pogo_bottom.stl

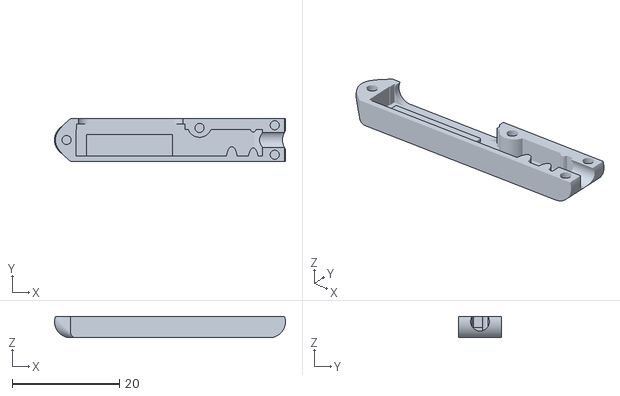
[picture p120: CAD file, 2023-04-01]
Production/3DPrint/pogo_bottom.stl
43.0 x 8.00 x 4.00
