whowechina/iidx_pico/Production/3DPrint/pogo_top.stl

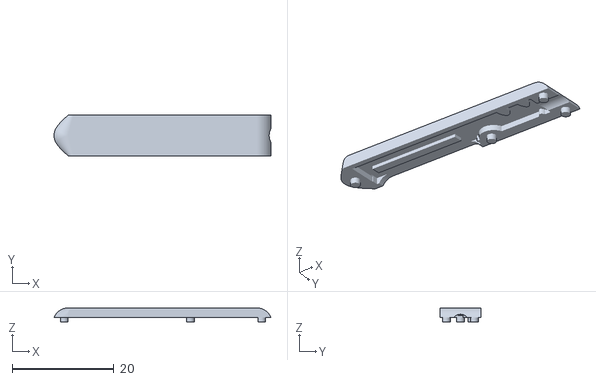
[picture p121: CAD file, 2023-04-01]
Production/3DPrint/pogo_top.stl
42.6 x 8.00 x 2.80
